djclarke92/nimrod/images/dead_robot.png

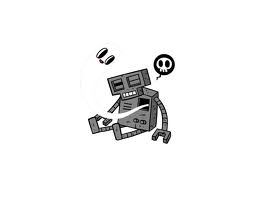
images/dead_robot.png
