djclarke92/nimrod/images/esp8266.png

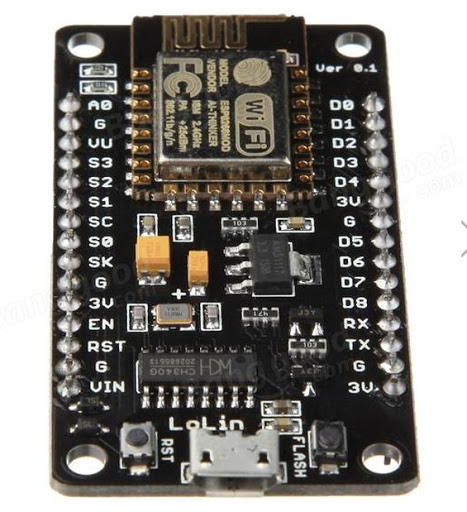
images/esp8266.png
