djclarke92/nimrod/images/eye.png

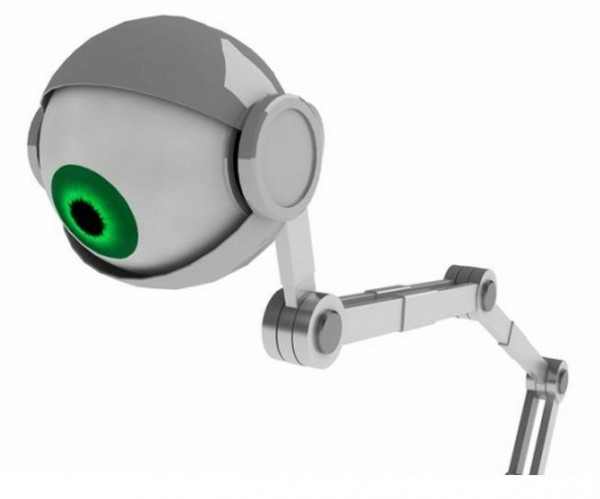
images/eye.png
