djclarke92/nimrod/images/green_tick.png

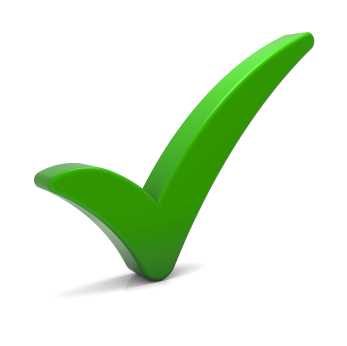
images/green_tick.png
