djclarke92/nimrod/images/inductor2.png

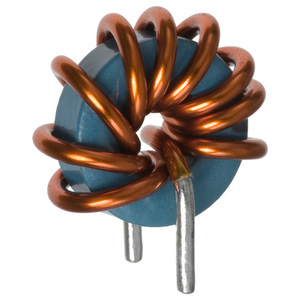
images/inductor2.png
