djclarke92/nimrod/images/questionmark.png

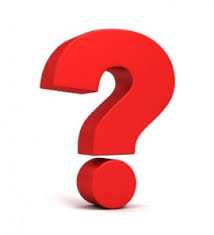
images/questionmark.png
