djclarke92/nimrod/images/usb-rs485.jpg

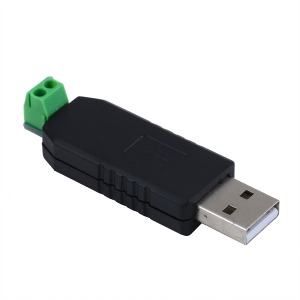
images/usb-rs485.jpg
