djclarke92/nimrod/images/WP3082ADAM.jpg

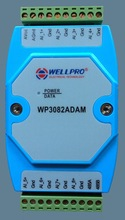
images/WP3082ADAM.jpg
