djclarke92/nimrod/images/WP8025ADAM.jpg

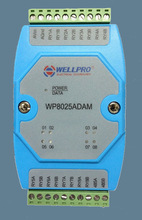
images/WP8025ADAM.jpg
