djclarke92/nimrod/bin/set-address.cpp

/*
 * Nimrod set-address utility: set the modbus address and baud rate on Wellpro modbus devices
 *
 */

#include <stdio.h>
#include <unistd.h>
#include <string.h>
#include <stdlib.h>
#include <errno.h>
#include <signal.h>
#include <stdarg.h>
#include <time.h>
#include <sys/stat.h>
#include <pthread.h>
#include <sys/wait.h>

#include <modbus/modbus.h>


int gRS485_iBaud = 9600;
char gRS485_cParity = 'N';
int gRS485_iDataBits = 8;
int gRS485_iStopBits = 1;


void SetNewAddress( modbus_t *ctx, int oldAddr, int newAddr, int oldBaud, int newBaud, int type, int vsdOperation );
void ReadData( modbus_t *ctx, int newAddr, int newBaud, int type, int vsdOperation, int vsdValue );


int main( int argc, char** argv )
{
	int type = 0;
	int oldAddr = 0;
	int newAddr = 0;
	int oldBaud = 9600;
	int newBaud = 9600;
	int vsdOperation = 0;
	int vsdValue = 0;
	modbus_t* ctx = NULL;

	printf( "Compiled against libmodbus v%s\n", LIBMODBUS_VERSION_STRING );
	printf( "Linked against libmodbus v%d.%d.%d\n", libmodbus_version_major, libmodbus_version_minor, libmodbus_version_micro );
	printf( "\n" );

	if ( argc >= 7 )
	{	// broadcast new address for ALL connected devices

		oldAddr = atoi( argv[2] );
		newAddr = atoi( argv[3] );
		oldBaud = atoi( argv[4] );
		newBaud = atoi( argv[5] );
		type = atoi( argv[6] );

		if ( argc >= 8 )
			vsdOperation = atoi(argv[7] );
		if ( argc >= 9 )
			vsdValue = atoi(argv[8] );

		gRS485_iBaud = oldBaud;

		ctx = modbus_new_rtu( argv[1], gRS485_iBaud, gRS485_cParity, gRS485_iDataBits, gRS485_iStopBits );
		if ( ctx == NULL )
		{
			printf( "Error: modbus ctx in is null, aborting: %s\n", modbus_strerror(errno) );
			exit( 1 );
		}

		modbus_set_debug(ctx, true);

		if ( modbus_connect(ctx) == -1 )
		{
			printf( "Error: modbus_connect() failed, aborting: %s\n", modbus_strerror(errno) );
			exit( 1 );
		}

		printf( "Ctx %p (vsdOp %d)\n", ctx, vsdOperation );


		SetNewAddress( ctx, oldAddr, newAddr, oldBaud, newBaud, type, vsdOperation );

		if ( oldBaud != newBaud )
		{
			modbus_free( ctx );
			ctx = NULL;

			gRS485_iBaud = newBaud;

			ctx = modbus_new_rtu( argv[1], gRS485_iBaud, gRS485_cParity, gRS485_iDataBits, gRS485_iStopBits );
			if ( ctx == NULL )
			{
				printf( "Error: modbus ctx in is null, aborting: %s\n", modbus_strerror(errno) );
				exit( 1 );
			}

			modbus_set_debug(ctx, true);

			if ( modbus_connect(ctx) == -1 )
			{
				printf( "Error: modbus_connect() failed, aborting: %s\n", modbus_strerror(errno) );
				exit( 1 );
			}

			printf( "Ctx %p, Baud Rate %d\n", ctx, newBaud );
		}

		ReadData( ctx, newAddr, newBaud, type, vsdOperation, vsdValue );


		modbus_free( ctx );
		ctx = NULL;
	}
	else
	{
		printf( "Usage: '%s <com_port> <old_addr> <new_addr> <old_baud> <new_baud> <device_type> [vsd_op] [vsd_val]' to set comms parameters\n", argv[0] );
		printf( "    where device_type: 0 Digital Input devices\n" );
		printf( "                       1 Digital Output devices\n" );
		printf( "                       2 Voltage device and temperature devices\n" );
		printf( "                       3 Thermocouple devices PD3064\n" );
		printf( "                       4 HDL300 water level sensor\n" );
		printf( "                       5 Rotary Encoder MT-5208 series\n" );
		printf( "                       6 PZEM-016 AC V/A Monitor\n" );
		printf( "                       7 NFlixen 9600 VSD\n" );
		printf( "                       8 Power Electronics SD700 VSD\n" );
		printf( "                       9 HDHK 8Ch Current Meter\n" );
		printf( "                      10 SHT40 / XY-MD02 Temperature/Humidity sensor\n" );
		printf( "                      11 PT113MB Load Cell Transmitter\n" );
		printf( "                      12 HPT604 level sensor\n" );
		printf( "                      13 HRS10 rain sensor\n" );
		printf( "    optional   vsd_op: 1 forward\n");
		printf( "                       2 backward\n");
		printf( "                       3 forward jog\n");
		printf( "                       4 backward jog\n");
		printf( "                       5 free stop\n");
		printf( "                       6 speed down stop\n");
		printf( "                       7 fault reset\n");
		printf( "                       8 set frequency\n");
		printf( "              vsd_val: xx frequency in Hz <= 50\n");
	}

	return 0;
}

// PT113MB - baud rate and address set by ATCom windows woftware only
// 0x03 read holding registers
// 0x10 preset multiple registers
// read 40001:	weight/force/count
// read 40003: status

// SHT40 / XY-MD02 Temperature/Humidity sensor
// input register 0x0001	Temprature, 2 bytes
// input register 0x0002	Humidity, 2 bytes
// output register 0x0101	Address, 2 bytes
// output register 0x0102	Baud Rate, 9600, 14400, 19200
// output register 0x0103	Temperature correction / 10, +10.0 - -10.0, 2 bytes
// output register 0x0104	Humidity correction / 10, +10.0 - -10.0, 2 bytes


// PZEM-016 AC V/I Monitor
// Does not reply to the broadcast address 0x00
// Uses read_input_registers()
// Only 9600 baud is supported
// Input Register 0x00 voltage, lsb = 0.1V
// Input Register 0x01/2 current, lsb = 0.001A
// Input Register 0x03/4 power, lsb = 0.1W
// Input Register 0x05/6 energy, lsb = 1Wh
// Input Register 0x07 frequency, lsb = 0.1Hz
// Input Register 0x08 power factor, lsb = 0.01
// Input Register 0x09 alarm status
// Register 0x01 power alarm threshold
// Register 0x02 address
//
// MT 5208 Rotary Encoder 12 bit
// function code 0x03 = read
// Register 0x00 angle
// Register 0x01 turns
// Register 0x02 address
// Register 0x03 baud rate (1=9600, 2=19200, 3=38400)
// Register 0x04 parity (1=N, 2=Odd, 3=even)
// Register 0x05 set zero pos (write data 0xff)
// Register 0x06 set counting dir (1=clockwise, 2=anticlockwise)
// Cable red = +12V
//       black = 0V
//       green = rs485A
//       yellow - rs486B
//       white = factory reset (connect to 0V during use)

// HDL300 water level sensor
// function code 0x03 = read
// Register 0x00 = modbus address
// Register 0x01 = baud rate
// Register 0x02 = pressure units (0=Mpa, 1= Kpa, 2=pa, 3=bar, 4=Mbar, 5=kg/cm2, 6= psi, 7=m h2o, 8=mm h2o)
// Register 0x03 = decimal place (0= xxxx, 1= xxx.x, 2= xx.xx, 3= x.xxx, 4= .xxxx)
// Register 0x04 = depth in units (-32768 to 32767)
// Cable red = +12V
//       black = 0V
//       white = rs485B
//       blue = rs485A

// PD30xx sereies devices (thermocouple)
// function code 0x03 = read, 0x06 = write
// Register 0x10: 0x01 (address) 0x00 (comms)
//		address		0x01 to 250
//		comms	bits 7:5 - 	0x00
//				bits 4:3 - 	00 = no parity
//							01 = even parity
//							10 = odd parity
//							11 = odd parity
//				bits 2:0 -	000=9600 	0
//							001=1200	1
//							010=2400	2
//							011=4800	3
//							100=9600	4
//							101=14400	5
//							110=19200	6
// Register 0x11: 0xff (round values) 0x05 (sample rate)
//		rounding		0xff
//		sample rate		0-255 seconds (0 same as 1)

// HDHK 8CH Current Meter
// function code 0x03 read single registers
// function code 0x06 write single register
// function code 0x10 write multiple registers
// register 0x0000 r/o - program version 650 = 6.50
// register 0x0001 r/o - current A-D (ch 01-04) channel range, unsigned int, 40 = 40A
// register 0x0002 r/o - current E-H (ch 05-08) channel range, unsigned int, 40 = 40A
// register 0x0003 r/w - address and baud rate, default 0x0001
//                       high byte high nibble:  0-3 N81, E81, O81, N82
//                       high byte low nibble: 0-8 9600, 1200, 2400, 4800, 9600, 19200, 38200, 57600, 115200
//                       low byte: module address
// register 0x0004 r/o - factory date - high byte year, low byte month
// register 0x0005 - reserved
// register 0x0006 r/w - freq division coefficient(1 - 5, def = 5), sample freq = 10Hz * 5 / coeff, sample freq = 400Hz
// register 0x0007 r/w -  high byte measurement result value, low byte is freq selection coefficient
// register 0x0008 - 0x000F r/o - channel A-H current, unsigned, 0.01A
// register 0x0010 - 0x0017 r/o - channel A-H frequency, unsigned, 0.1Hz
// register 0x0018 - 0x001F r/w - channel A-H current transformer ratio, unsigned 

// HPT604 level sensor
// register 0x0000 2 bytes, sensor type 0-65535
// register 0x0001 2 bytes, address 1-255
// register 0x0002 2 bytes, baud rate 0=19200, 1=9600, 2=4800, 3=2400, 4=1200
// register 0x0003 2 bytes, parity, 0=O, 1=N, 2=E
// register 0x0004 2 bytes, density of medium 1000=water
// register 0x0007 2 bytes, display level unit 16=m, 17=cm, 18=mm
// register 0x0013 4 bytes, level value
// register 0x0015 2 bytes, decimal points of level display

// HRS10 rain sensor - default address 0x01, default baud 4800
// register 0x0000 2 bytes, 10 actual value in mm
// register 0x0000 2 bytes, clear rainfall data semd 0x00 ox5A
// register 0x07D0 2 bytes, modbus address
// retuster 0x07D1 2 bytes, baud rate (0=2400, 1=4800, 2=9600, 3=19200, 4=38400, 5=57600, 6=115200, 7=1200) 

void SetNewAddress( modbus_t *ctx, int oldAddr, int newAddr, int oldBaud, int newBaud, int type, int vsdOperation )
{
	bool bBaudOk = true;
	int modBaud = 2;
	int modBaud2 = 0;
	int modBaud3 = 0;
	int modBaud4 = 0;
	int modBaud5 = 0;
	int modBaudHDHK = 0;
	int modBaudHPT604 = 0;
	int modBaudHRS10 = 0;
	int reg;

	// check the baud rate
	switch ( newBaud )
	{
	default:
		bBaudOk = false;
		break;
	case 4800:
		modBaud = 1;
		modBaud2 = 3;
		modBaud4 = 2;
		modBaudHDHK = 3;
		modBaudHPT604 = 2;
		modBaudHRS10 = 1;
		break;
	case 9600:		// no baud rate change
		modBaud = 2;
		modBaud2 = 0;
		modBaud4 = 3;
		modBaud5 = 1;
		modBaudHDHK = 0;
		modBaudHPT604 = 1;
		modBaudHRS10 = 2;
		break;
	case 19200:
		modBaud = 3;
		modBaud2 = 6;
		modBaud4 = 4;
		modBaud5 = 2;
		modBaudHDHK = 5;
		modBaudHPT604 = 0;
		modBaudHRS10 = 3;
		break;
	}

	switch ( oldBaud )
	{
	default:
		break;
	case 4800:
		modBaud3 = 3;
		break;
	case 9600:		// no baud rate change
		modBaud3 = 0;
		break;
	case 19200:
		modBaud3 = 6;
		break;
	}

	if ( newAddr <= 0x00 || newAddr > 0xfe )
	{	// error
		printf( "Error: Invalid new address %d\n", newAddr );
	}
	else if ( !bBaudOk )
	{
		printf( "Error: Invalid new baud rate %d\n", newBaud );
	}
	else if ( newAddr == oldAddr && newBaud == oldBaud && vsdOperation == 0 )
	{
		printf( "Nothing to set 0x%02x, %d\n", newAddr, newBaud );
	}
	else
	{	// data is valid

		// MODBUS_BROADCAST_ADDRESS;
		if ( modbus_set_slave( ctx, oldAddr ) == -1 )
		{
			printf( "Error: modbus_set_slave(%d) failed: %s\n", oldAddr, modbus_strerror(errno) );
		}


		if ( type == 0 || type == 1 || type == 2 )
		{
			if ( newAddr != oldAddr )
			{
				printf( "Setting new address 0x%02x -> 0x%02x\n", oldAddr, newAddr );

				reg = 0x64;
				if ( modbus_write_register( ctx, reg, newAddr ) == -1 )
				{
					printf( "Error: modbus_write_register(0x%x) failed: %s\n", reg, modbus_strerror(errno) );
				}
				else
				{
					printf( "New slave address 0x%02x set\n", newAddr );

					if ( modbus_set_slave( ctx, newAddr ) == -1 )
					{
						printf( "Error: modbus_set_slave(%d) failed: %s\n", newAddr, modbus_strerror(errno) );
					}
				}
			}
			else
			{
				printf( "Warning: skip setting module address\n" );
			}

			if ( newBaud != oldBaud )
			{
				printf( "Setting new baud rate %d -> %d (%d)\n", oldBaud, newBaud, modBaud );

				reg = 0x65;
				if ( modbus_write_register( ctx, reg, modBaud ) == -1 )
				{
					printf( "Error: modbus_write_register(0x%x) failed: %s\n", reg, modbus_strerror(errno) );
				}
				else
				{
					printf( "New baud rate %d set\n", newBaud );
				}
			}
		}
		else if ( type == 3 )
		{	// thermocouple
			if ( newAddr != oldAddr )
			{
				int val = modBaud3;	// 0x00 = 9600 baud in low byte

				val += (newAddr << 8);

				printf( "Setting new address 0x%02x -> 0x%02x (0x%x)\n", oldAddr, newAddr, val );

				reg = 0x10;
				if ( modbus_write_register( ctx, reg, val ) == -1 )
				{
					printf( "Error: modbus_write_register(0x%x) failed: %s\n", reg, modbus_strerror(errno) );
				}
				else
				{
					printf( "New slave address 0x%02x set\n", newAddr );

					if ( modbus_set_slave( ctx, newAddr ) == -1 )
					{
						printf( "Error: modbus_set_slave(%d) failed: %s\n", newAddr, modbus_strerror(errno) );
					}
				}
			}
			else
			{
				printf( "Warning: skip setting module address\n" );
			}

			if ( newBaud != oldBaud )
			{
				int val = modBaud2;
				val += (newAddr << 8);

				printf( "Setting new baud rate %d -> %d (%d,0x%x)\n", oldBaud, newBaud, modBaud2, val );

				reg = 0x10;
				if ( modbus_write_register( ctx, reg, val ) == -1 )
				{
					printf( "Error: modbus_write_register(0x%x) failed: %s\n", reg, modbus_strerror(errno) );
				}
				else
				{
					printf( "New baud rate %d set\n", newBaud );
				}
			}
		}
		else if ( type == 4 )
		{	// HDL300 level sensor

			if ( newAddr != oldAddr )
			{
				printf( "Setting new address 0x%02x -> 0x%02x\n", oldAddr, newAddr );

				// HDL300 modbus address is in register 0x00
				reg = 0x00;
				if ( modbus_write_register( ctx, reg, newAddr ) == -1 )
				{
					printf( "Error: modbus_write_register(0x%x) failed: %s\n", reg, modbus_strerror(errno) );
				}
				else
				{
					printf( "New slave address 0x%02x set\n", newAddr );

					if ( modbus_set_slave( ctx, newAddr ) == -1 )
					{
						printf( "Error: modbus_set_slave(%d) failed: %s\n", newAddr, modbus_strerror(errno) );
					}
				}
			}
			else
			{
				printf( "Warning: skip setting module address\n" );
			}

			if ( newBaud != oldBaud )
			{
				printf( "Setting new baud rate %d -> %d (%d)\n", oldBaud, newBaud, modBaud4 );

				reg = 0x1;
				if ( modbus_write_register( ctx, reg, modBaud4 ) == -1 )
				{
					printf( "Error: modbus_write_register(0x%x) failed: %s\n", reg, modbus_strerror(errno) );
				}
				else
				{
					printf( "New baud rate %d set\n", newBaud );
				}
			}

			if ( newAddr != oldAddr || newBaud != oldBaud )
			{	// write changes to eeprom
				usleep( 50000 );

				reg = 0x0f;
				if ( modbus_write_register( ctx, reg, 0x0000) == -1 )
				{
					printf( "Error: modbus_write_register(0x%x) failed: %s\n", reg, modbus_strerror(errno) );
				}
				else
				{
					printf( "Changes saved\n" );
				}

				usleep( 200000 );
			}
		}
		else if ( type == 5 )
		{	// rotary encoder
			if ( newAddr != oldAddr )
			{
				printf( "Setting new address 0x%02x -> 0x%02x\n", oldAddr, newAddr );

				// MT-5208 modbus address is in register 0x02
				reg = 0x02;
				if ( modbus_write_register( ctx, reg, newAddr ) == -1 )
				{
					printf( "Error: modbus_write_register(0x%x) failed: %s\n", reg, modbus_strerror(errno) );
				}
				else
				{
					printf( "New slave address 0x%02x set\n", newAddr );

					if ( modbus_set_slave( ctx, newAddr ) == -1 )
					{
						printf( "Error: modbus_set_slave(%d) failed: %s\n", newAddr, modbus_strerror(errno) );
					}
				}
			}
			else
			{
				printf( "Warning: skip setting module address\n" );
			}

			if ( newBaud != oldBaud )
			{
				printf( "Setting new baud rate %d -> %d (%d)\n", oldBaud, newBaud, modBaud5 );

				reg = 0x03;
				if ( modbus_write_register( ctx, reg, modBaud5 ) == -1 )
				{
					printf( "Error: modbus_write_register(0x%x) failed: %s\n", reg, modbus_strerror(errno) );
				}
				else
				{
					printf( "New baud rate %d set\n", newBaud );
				}
			}
		}
		else if ( type == 6 )
		{	// PZEM-016 AC V/I Monitor
			if ( newAddr != oldAddr )
			{
				printf( "Setting new address 0x%02x -> 0x%02x\n", oldAddr, newAddr );

				// MT-5208 modbus address is in register 0x02
				reg = 0x02;
				if ( modbus_write_register( ctx, reg, newAddr ) == -1 )
				{
					printf( "Error: modbus_write_register(0x%x) failed: %s\n", reg, modbus_strerror(errno) );
				}
				else
				{
					printf( "New slave address 0x%02x set\n", newAddr );

					if ( modbus_set_slave( ctx, newAddr ) == -1 )
					{
						printf( "Error: modbus_set_slave(%d) failed: %s\n", newAddr, modbus_strerror(errno) );
					}
				}
			}
			else
			{
				printf( "Warning: skip setting module address\n" );
			}

			if ( newBaud != oldBaud )
			{
				printf( "Only supports 9600 baud %d\n", oldBaud );
			}
		}
		else if ( type == 7 || type == 8 )
		{	// NFlixen VSD - baud rate set on the VSD
			// Power Electronics VSD
			if ( newBaud != oldBaud )
			{
				printf( "Ignoring baud rate change\n" );
			}
		}
		else if ( type == 9 )
		{	// HDHK 8Ch current meter
			if ( newAddr != oldAddr || newBaud != oldBaud )
			{
				reg = 0x0003;

				uint16_t parms = ((0x00 * 0x0f) << 12);	// N81
				uint16_t val = parms + ((modBaudHDHK & 0x0f) << 8) + parms + (newAddr & 0xff);

				if ( modbus_write_register( ctx, reg, val ) == -1 )
				{
					printf( "Error: modbus_write_register(0x%x) failed: %s\n", reg, modbus_strerror(errno) );
				}
				else
				{
					if ( newAddr != oldAddr )
					{
						printf( "New slave address 0x%02x set\n", newAddr );

						if ( modbus_set_slave( ctx, newAddr ) == -1 )
						{
							printf( "Error: modbus_set_slave(%d) failed: %s\n", newAddr, modbus_strerror(errno) );
						}
					}
					if ( newBaud != oldBaud )
					{
						printf( "New baud rate %d set, sleep 3 sec\n", newBaud );
						usleep( 3000000 );
					}
				}

				usleep( 50000 );
			}
		}
		else if ( type == 10 )
		{	// SHT40 / XY-MD02 temperature/humidity sensor
			if ( newAddr != oldAddr || newBaud != oldBaud )
			{
				reg = 0x0101;

				uint16_t val[2];

				val[0] = newAddr;
				switch ( newBaud )
				{
				default:
				case 9600:
					val[1] = 9600;
					break;
				case 14400:
					val[1] = 14400;
					break;
				case 19200:
					val[1] = 19200;
					break;
				}

				if ( modbus_write_registers( ctx, reg, 2, val ) == -1 )
				{
					printf( "Error: modbus_write_register(0x%x) failed: %s\n", reg, modbus_strerror(errno) );
				}
				else if ( newAddr == oldAddr )
				{
					printf( "New baud rate %d set\n", newBaud );
				}
				else if ( newBaud == oldBaud )
				{
					printf( "New slave address 0x%02d set\n", newAddr );
				}
				else
				{
					printf( "New slave address 0x%02d set\n", newAddr );
					printf( "New baud rate %d set\n", newBaud );
				}
			}

			// must power cycle the device when changing the address of baud rate
			if ( newAddr != oldAddr || newBaud != oldBaud )
			{
				printf( "\nXY-MD02 device does NOT listen to broadcast address 0x00, default addr is 0x01\n" );
				printf( "\nPower cycle the device to set the new address / baud rate\nPress enter when done\n");
				getc(stdin);
			}
		}
		else if ( type == 11 )
		{
			printf( "skip baud/address setting for PT113MB\n" );
		}
		else if ( type == 12 )
		{	// HPT602 level sensor

			if ( newAddr != oldAddr )
			{
				printf( "Setting new address 0x%02x -> 0x%02x\n", oldAddr, newAddr );

				// HPT604 modbus address is in register 0x0001
				reg = 0x01;
				if ( modbus_write_register( ctx, reg, newAddr ) == -1 )
				{
					printf( "Error: modbus_write_register(0x%x) failed: %s\n", reg, modbus_strerror(errno) );
				}
				else
				{
					printf( "New slave address 0x%02x set\n", newAddr );

					if ( modbus_set_slave( ctx, newAddr ) == -1 )
					{
						printf( "Error: modbus_set_slave(%d) failed: %s\n", newAddr, modbus_strerror(errno) );
					}
				}
			}
			else
			{
				printf( "Warning: skip setting module address\n" );
			}

			if ( newBaud != oldBaud )
			{
				printf( "Setting new baud rate %d -> %d (%d)\n", oldBaud, newBaud, modBaudHPT604 );

				reg = 0x02;
				if ( modbus_write_register( ctx, reg, modBaudHPT604 ) == -1 )
				{
					printf( "Error: modbus_write_register(0x%x) failed: %s\n", reg, modbus_strerror(errno) );
				}
				else
				{
					printf( "New baud rate %d set\n", newBaud );
				}
			}
		}
		else if ( type == 13 )
		{	// HRS10 rain sensor sensor

			if ( newAddr != oldAddr )
			{
				printf( "Setting new address 0x%02x -> 0x%02x\n", oldAddr, newAddr );

				// HPT604 modbus address is in register 0x0001
				reg = 0x07D0;
				if ( modbus_write_register( ctx, reg, newAddr ) == -1 )
				{
					printf( "Error: modbus_write_register(0x%x) failed: %s\n", reg, modbus_strerror(errno) );
				}
				else
				{
					printf( "New slave address 0x%02x set\n", newAddr );

					if ( modbus_set_slave( ctx, newAddr ) == -1 )
					{
						printf( "Error: modbus_set_slave(%d) failed: %s\n", newAddr, modbus_strerror(errno) );
					}
				}
			}
			else
			{
				printf( "Warning: skip setting module address\n" );
			}

			if ( newBaud != oldBaud )
			{
				printf( "Setting new baud rate %d -> %d (%d)\n", oldBaud, newBaud, modBaudHRS10 );

				reg = 0x07D1;
				if ( modbus_write_register( ctx, reg, modBaudHRS10 ) == -1 )
				{
					printf( "Error: modbus_write_register(0x%x) failed: %s\n", reg, modbus_strerror(errno) );
				}
				else
				{
					printf( "New baud rate %d set\n", newBaud );
				}
			}
		}
		else
		{
			printf( "Error: invalid type = %d\n", type );
		}
	}

	usleep( 30000 );
}

void ReadData( modbus_t *ctx, int newAddr, int newBaud, int type, int vsdOperation, int vsdValue )
{
	int rc;
	int addr;
	int iLen = 8;

	if ( type == 0 )
	{
		printf( "Setting slave addr to %d\n", newAddr );
		if ( modbus_set_slave( ctx, newAddr ) == -1 )
		{
			printf( "Error: modbus_set_slave(%d) failed: %s\n", newAddr, modbus_strerror(errno) );
		}

		usleep( 30000 );

		// read input bits to see if the device is talking
		addr = 0;
		uint8_t uInputs[iLen];

		for ( int i = 0; i < iLen; i++ )
		{
			uInputs[i] = 0;
		}

		rc = modbus_read_input_bits( ctx, addr, iLen, uInputs );
		if ( rc == -1 )
		{
			printf( "Error: modbus_read_input_bits() failed: %s\n", modbus_strerror(errno) );
		}
		else
		{
			printf( "Read registers: " );
			for ( int i = 0; i < iLen; i++ )
			{
				printf( "%u ", uInputs[i] );
			}
			printf ( "\n" );
		}
	}
	else if ( type == 1 )
	{	// output
		printf( "Setting slave addr to %d\n", newAddr );
		if ( modbus_set_slave( ctx, newAddr ) == -1 )
		{
			printf( "Error: modbus_set_slave(%d) failed: %s\n", newAddr, modbus_strerror(errno) );
		}

		usleep( 30000 );

		printf( "modbus_write_bit() 1 -> 1\n" );
		if ( modbus_write_bit( ctx, 1, true ) == -1 )
		{	// failed
			printf( "Error: modbus_write_bit() failed: %s\n", modbus_strerror(errno) );
		}
		else
		{
			printf( "Bit 1 turned on\n" );
		}
		usleep( 500000 );

		uint8_t cData[16];
		printf( "modbus_read_bits()\n" );
		if ( modbus_read_bits( ctx, 0, 16, cData ) == -1 )
		{	// error
			printf( "Error: modbus_read_bits() failed: %s\n", modbus_strerror(errno) );
		}
		else
		{
			printf( "Read bits: " );
			for ( int i = 0; i < iLen; i++ )
			{
				printf( "%u ", (uint8_t)cData[i] );
			}
			printf ( "\n" );
		}

		usleep( 30000 );

		printf( "modbus_write_bit() 1 -> 0\n" );
		if ( modbus_write_bit( ctx, 1, false ) == -1 )
		{	// failed
			printf( "Error: modbus_write_bit() failed: %s\n", modbus_strerror(errno) );
		}
		else
		{
			printf( "Bit 1 turned off\n" );
		}
	}
	else if ( type == 2 )
	{	// voltage
		printf( "Setting slave addr to %d\n", newAddr );
		if ( modbus_set_slave( ctx, newAddr ) == -1 )
		{
			printf( "Error: modbus_set_slave(%d) failed: %s\n", newAddr, modbus_strerror(errno) );
		}

		addr = 0x00;
		uint16_t ulInputs[iLen];

		rc = modbus_read_registers( ctx, addr, iLen, ulInputs );
		if ( rc == -1 )
		{
			printf( "Error: modbus_read_registers() failed: %s\n", modbus_strerror(errno) );
		}
		else
		{
			printf( "Read registers: " );
			for ( int i = 0; i < iLen; i++ )
			{
				printf( "%u ", ulInputs[i] );
			}
			printf ( "\n" );
		}
	}
	else if ( type == 3 )
	{	// thermocouple
		printf( "Setting slave addr to %d\n", newAddr );
		if ( modbus_set_slave( ctx, newAddr ) == -1 )
		{
			printf( "Error: modbus_set_slave(%d) failed: %s\n", newAddr, modbus_strerror(errno) );
		}

		addr = 0x20;
		uint16_t ulInputs[iLen];

		rc = modbus_read_registers( ctx, addr, iLen, ulInputs );
		if ( rc == -1 )
		{
			printf( "Error: modbus_read_registers() failed: %s\n", modbus_strerror(errno) );
		}
		else
		{
			printf( "Read registers: " );
			for ( int i = 0; i < iLen; i++ )
			{
				printf( "%u ", ulInputs[i] );
			}
			printf ( "\n" );
		}
	}
	else if ( type == 4 )
	{	// hdl300 water level
		printf( "Setting slave addr to %d\n", newAddr );
		if ( modbus_set_slave( ctx, newAddr ) == -1 )
		{
			printf( "Error: modbus_set_slave(%d) failed: %s\n", newAddr, modbus_strerror(errno) );
		}

		uint16_t ulInputs[iLen];

		int iFactor = 1;

		iLen = 2;
		addr = 0x02;
		rc = modbus_read_registers( ctx, addr, iLen, ulInputs );
		if ( rc == -1 )
		{
			printf( "Error: modbus_read_registers() failed: %s\n", modbus_strerror(errno) );
		}
		else
		{
			printf( "Read registers: 0x%02x (units)  0x%02x (decimal)\n", ulInputs[0], ulInputs[1] );
			
			// TODO: iFactor needs to change depending on what units are being read. This code assume units=7 (m h2o)
			// check decimal point
			switch ( ulInputs[1] )
			{
			default:
				break;
			case 0:	// xxxx
				iFactor = 1000;
				break;
			case 1:	// xxx.x
				iFactor = 100;
				break;
			case 2:	// xx.xx
				iFactor = 10;
				break;
			case 3:	// x.xxx
				iFactor = 1;
				break;
			}
		}

		addr = 0x04;

		rc = modbus_read_registers( ctx, addr, iLen, ulInputs );
		if ( rc == -1 )
		{
			printf( "Error: modbus_read_registers() failed: %s\n", modbus_strerror(errno) );
		}
		else
		{
			printf( "Read registers: " );
			for ( int i = 0; i < iLen; i++ )
			{
				printf( "%u ", ulInputs[i] );
			}
			printf ( "\n" );
			printf( "Depth = %d mm\n", ulInputs[0] * iFactor );
		}

		usleep( 50000 );

	}
	else if ( type == 5 )
	{	// rotary encoder
		printf( "Setting slave addr to %d\n", newAddr );
		if ( modbus_set_slave( ctx, newAddr ) == -1 )
		{
			printf( "Error: modbus_set_slave(%d) failed: %s\n", newAddr, modbus_strerror(errno) );
		}

		iLen = 5;

		addr = 0x00;
		uint16_t ulInputs[iLen];

		rc = modbus_read_registers( ctx, addr, iLen, ulInputs );
		if ( rc == -1 )
		{
			printf( "Error: modbus_read_registers() failed: %s\n", modbus_strerror(errno) );
		}
		else
		{
			printf( "Read registers: " );
			for ( int i = 0; i < iLen; i++ )
			{
				printf( "%u ", ulInputs[i] );
			}
			printf ( "\n" );
			printf( "Angle %d (%.1f deg), Turns %d\n", ulInputs[0], 360 * (double)ulInputs[0]/4096, ulInputs[1] );
		}
	}
	else if ( type == 6 )
	{	// PZEM-016 AC V/A Monitor
		printf( "Setting slave addr to %d\n", newAddr );
		if ( modbus_set_slave( ctx, newAddr ) == -1 )
		{
			printf( "Error: modbus_set_slave(%d) failed: %s\n", newAddr, modbus_strerror(errno) );
		}

		iLen = 10;

		addr = 0x00;
		uint16_t ulInputs[iLen];

		rc = modbus_read_input_registers( ctx, addr, iLen, ulInputs );
		if ( rc == -1 )
		{
			printf( "Error: modbus_read_registers() failed: %s\n", modbus_strerror(errno) );
		}
		else
		{
			printf( "Read registers: " );
			for ( int i = 0; i < iLen; i++ )
			{
				printf( "%u ", ulInputs[i] );
			}
			printf ( "\n" );
			printf( "V=%.1fV, I=%.2fA, P=%.0fW, E=%dWh, F=%.1fHz, PF=%.1f, Alrm=%d\n", (double)ulInputs[0] / 10, (double)(ulInputs[1] + (ulInputs[2]>>8)) / 1000, (double)(ulInputs[3] + (ulInputs[4]>>8)) / 10,
					(int)(ulInputs[5] + (ulInputs[6]>>8)), (double)ulInputs[7] / 10, (double)ulInputs[8] / 100, ulInputs[9] );
		}
	}
	else if ( type == 7 )
	{	// NFlixen VSD
		int iSleep = 50000;
		printf( "Setting slave addr to %d\n", newAddr );
		if ( modbus_set_slave( ctx, newAddr ) == -1 )
		{
			printf( "Error: modbus_set_slave(%d) failed: %s\n", newAddr, modbus_strerror(errno) );
		}

		iLen = 18;

		addr = 0x1001;
		uint16_t ulInputs[iLen];

		rc = modbus_read_registers( ctx, addr, iLen, ulInputs );
		if ( rc == -1 )
		{
			printf( "Error: modbus_read_registers() failed: %s\n", modbus_strerror(errno) );
		}
		else
		{
			printf( "Read registers: " );
			for ( int i = 0; i < iLen; i++ )
			{
				printf( "%u ", ulInputs[i] );
			}
			printf ( "\n" );
			printf( "F=%.2fHz, BV=%.1fV, MV=%.1fV, MA=%.1fA, MP=%.2fkW, MT=%.1f%%, RS=%.1frpm\n",
					(double)ulInputs[0] / 100,	// 0.01 Hz
					(double)ulInputs[1] / 10, 	// 0.1 V
					(double)ulInputs[2],		// 1 V
					(double)ulInputs[3] / 10, 	// 0.1 A ??
					(double)ulInputs[4] / 100,	// 0.1 kW ??
					(double)ulInputs[5] / 10, 	// 0.1 %
					(double)ulInputs[6] );		// 1
		}
		printf("\n");

		usleep( iSleep );

		// output current
		iLen = 1;
		addr = 0x7004;
		rc = modbus_read_registers( ctx, addr, iLen, ulInputs );
		if ( rc == -1 )
		{
			printf( "Error: modbus_read_registers() failed: %s\n", modbus_strerror(errno) );
		}
		else
		{
				printf( "Read Output Current: %d %.1f A\n", (int)ulInputs[0], (double)ulInputs[0] / 10 );
		}
		printf("\n");

		usleep( iSleep );

		// status 
		iLen = 1;
		addr = 0x3000;

		rc = modbus_read_registers( ctx, addr, iLen, ulInputs );
		if ( rc == -1 )
		{
			printf( "Error: modbus_read_registers() failed: %s\n", modbus_strerror(errno) );
		}
		else
		{
			if ( ulInputs[0] == 1 )
				printf( "Read status: %d Forward\n", (int)ulInputs[0] );
			else if ( ulInputs[0] == 2 )
				printf( "Read status: %d Reverse\n", (int)ulInputs[0] );
			else if ( ulInputs[0] == 3 )
				printf( "Read status: %d Stopped\n", (int)ulInputs[0] );
			else
				printf( "Read status: %d Unknown\n", (int)ulInputs[0] );
		}
		printf("\n");

		usleep( iSleep );

		// fault code
		iLen = 1;
		addr = 0x8000;

		rc = modbus_read_registers( ctx, addr, iLen, ulInputs );
		if ( rc == -1 )
		{
			printf( "Error: modbus_read_registers() failed: %s\n", modbus_strerror(errno) );
		}
		else
		{
			printf( "Read fault code: %d\n", (int)ulInputs[0] );
		}
		printf("\n");

		if ( vsdOperation >= 1 && vsdOperation <= 7 )
		{	// vsd must be set for communications control P0-02 = 2
			// P0-03 = 9 for frequency control by communications
			usleep( iSleep );

			addr = 0x2000;

			rc = modbus_write_register( ctx, addr, vsdOperation );
			if ( rc == -1 )
			{
				printf( "Error: modbus_write_register() failed: %s\n", modbus_strerror(errno) );
			}
			else
			{
				printf( "VSD operation set to %d\n", vsdOperation );
			}
		}
		else if ( vsdOperation == 8 )
		{	// set frequency
			// value is % * 100 of max frequency (50Hz)
			usleep( iSleep );

			addr = 0x1000;

			int val = 10000 * ((double)vsdValue / 50);
			if ( val > 10000 )
				val = 10000;

			rc = modbus_write_register( ctx, addr, val );
			if ( rc == -1 )
			{
				printf( "Error: modbus_write_register() failed: %s\n", modbus_strerror(errno) );
			}
			else
			{
				printf( "VSD operation set to %d, %d Hz -> %d\n", vsdOperation, vsdValue, val );
			}
		}
	}
	else if ( type == 8 )
	{	// Power Electronics VSD
		printf( "Setting slave addr to %d\n", newAddr );
		if ( modbus_set_slave( ctx, newAddr ) == -1 )
		{
			printf( "Error: modbus_set_slave(%d) failed: %s\n", newAddr, modbus_strerror(errno) );
		}

		iLen = 9;

		addr = 40162;
		uint16_t ulInputs[iLen];

		// 0 40162: speed reference, 8192 = 100%
		// 1 40163: motor current, A / 10
		// 2 40164: motor torque, 8192 = 100%
		// 3 40165: motor power, kW / 10
		// 4 40166: motor voltage, V
		// 5 40167: motor frequency, Hz
		// 6 40168: motor power factor, pf /10
		// 7 40169: motor speed, rpm
		// 8 40170: motor speed, 8192 = 100%

		rc = modbus_read_registers( ctx, addr, iLen, ulInputs );
		if ( rc == -1 )
		{
			printf( "Error: modbus_read_registers() failed: %s\n", modbus_strerror(errno) );
		}
		else
		{
			printf( "Read registers: " );
			for ( int i = 0; i < iLen; i++ )
			{
				printf( "%u ", ulInputs[i] );
			}
			printf ( "\n" );
			printf( "F=%.2fHz, MV=%.1fV, MA=%.1fA, MP=%.2fkW, MT=%.1f%%, RS=%.1frpm\n",
					(double)ulInputs[5],		// Hz
					(double)ulInputs[4], 		// V
					(double)ulInputs[1] / 10,	// 0.1 A
					(double)ulInputs[3] / 10,	// 0.1 kW ??
					100 * (double)ulInputs[2] / 8192, 	// %
					(double)ulInputs[7] );		// rpm
		}
		printf("\n");

		usleep( 50000 );

		if ( vsdOperation >= 1 && vsdOperation <= 7 )
		{	// vsd must be set for communications control
			printf( "VSD operation not supported\n" );
		}
	}
	else if ( type == 9 )
	{	// HDHK 8Ch current meter
		printf( "Setting slave addr to %d\n", newAddr );
		if ( modbus_set_slave( ctx, newAddr ) == -1 )
		{
			printf( "Error: modbus_set_slave(%d) failed: %s\n", newAddr, modbus_strerror(errno) );
		}

		iLen = 8;
		uint16_t ulInputs[iLen];

		// read address and baud rate
		addr = 0x0000;
		rc = modbus_read_registers( ctx, addr, iLen, ulInputs );
		if ( rc == -1 )
		{
			printf( "Error: modbus_read_registers() failed: %s\n", modbus_strerror(errno) );
		}
		else
		{
			printf( "Version %.2f\n", (double)ulInputs[0] / 100 );
			printf( "Channel A-D range %dA\n", ulInputs[1] );
			printf( "Channel E-H range %dA\n", ulInputs[1] );
			printf( "Baud Rate %d\n", ((ulInputs[3] & 0x0f00) >> 8) );
			printf( "Address %d\n", (ulInputs[3] & 0x00ff) );
			printf( "Freq Div Coeff %d\n", ulInputs[6] );
		}

		addr = 0x0008;	
		rc = modbus_read_registers( ctx, addr, iLen, ulInputs );
		if ( rc == -1 )
		{
			printf( "Error: modbus_read_registers() failed: %s\n", modbus_strerror(errno) );
		}
		else
		{
			printf( "Read registers: " );
			for ( int i = 0; i < iLen; i++ )
			{
				printf( "%.2fA ", (double)ulInputs[i] / 100 );
			}
			printf ( " current\n" );
		}

		usleep( 30000 );

		addr = 0x0010;	
		rc = modbus_read_registers( ctx, addr, iLen, ulInputs );
		if ( rc == -1 )
		{
			printf( "Error: modbus_read_registers() failed: %s\n", modbus_strerror(errno) );
		}
		else
		{
			printf( "Read registers: " );
			for ( int i = 0; i < iLen; i++ )
			{
				printf( "%.1fHz ", (double)ulInputs[i] / 10 );
			}
			printf ( " measurement frequency\n" );
		}

		usleep( 30000 );

		addr = 0x0018;	
		rc = modbus_read_registers( ctx, addr, iLen, ulInputs );
		if ( rc == -1 )
		{
			printf( "Error: modbus_read_registers() failed: %s\n", modbus_strerror(errno) );
		}
		else
		{
			printf( "Read registers: " );
			for ( int i = 0; i < iLen; i++ )
			{
				printf( "%u ", ulInputs[i] );
			}
			printf ( " current transformer ratio\n" );
		}	
	}
	else if ( type == 10 )
	{	// SHT40 / XY-MD02 temperature / humidity sensor
		printf( "Setting slave addr to %d\n", newAddr );
		if ( modbus_set_slave( ctx, newAddr ) == -1 )
		{
			printf( "Error: modbus_set_slave(%d) failed: %s\n", newAddr, modbus_strerror(errno) );
		}

		iLen = 1;
		uint16_t ulInputs[iLen];
		addr = 0x0001;	
		rc = modbus_read_input_registers( ctx, addr, iLen, ulInputs );
		if ( rc == -1 )
		{
			printf( "Error: modbus_read_input_registers() failed: %s\n", modbus_strerror(errno) );
		}
		else
		{
			printf( "Temperature = %.1f degC\n", (double)((int)ulInputs[0]) / 10 );
		}

		addr = 0x0002;	
		rc = modbus_read_input_registers( ctx, addr, iLen, ulInputs );
		if ( rc == -1 )
		{
			printf( "Error: modbus_read_input_registers() failed: %s\n", modbus_strerror(errno) );
		}
		else
		{
			printf( "Humidity = %.1f %%\n", (double)ulInputs[0] / 10 );
		}
	}
	else if ( type == 11 )
	{	// PT113MB load cell transmitter
		printf( "Setting slave addr to %d\n", newAddr );
		if ( modbus_set_slave( ctx, newAddr ) == -1 )
		{
			printf( "Error: modbus_set_slave(%d) failed: %s\n", newAddr, modbus_strerror(errno) );
		}

		// read the psu voltage
		iLen = 1;
		uint16_t ulInputs[iLen];
		addr = 33;	
		rc = modbus_read_registers( ctx, addr, iLen, ulInputs );
		if ( rc == -1 )
		{
			printf( "Error: modbus_read_registers() failed: %s\n", modbus_strerror(errno) );
		}
		else
		{
			printf( "PSU Voltage %.1f V\n", ((double)ulInputs[0])/10 );
		}

		// read the status
		iLen = 1;
		//uint16_t ulInputs[iLen];
		addr = 2;	
		rc = modbus_read_registers( ctx, addr, iLen, ulInputs );
		if ( rc == -1 )
		{
			printf( "Error: modbus_read_registers() failed: %s\n", modbus_strerror(errno) );
		}
		else
		{
			printf( "Status 0x%04X\n", ulInputs[0] );
			printf( "System %s\n", ((ulInputs[0] & 0x0001) == 0 ? "Ready" : "Busy") );
			printf( "%s\n", ((ulInputs[0] & 0x0002) == 0 ? "Error" : "Data Ok") );
			printf( "Weight %s\n", ((ulInputs[0] & 0x0003) == 0 ? "Stable" : "Unstable") );
			printf( "%s Mode\n", ((ulInputs[0] & 0x0004) == 0 ? "Gross" : "Net") );
			printf( "%s Mode\n", ((ulInputs[0] & 0x0006) == 0 ? "Weight/Force" : "Count") );
			printf( "%s centre of zero\n", ((ulInputs[0] & 0x1000) == 0 ? "Out of" : "Weight is in") );
			printf( "Error Code %s (%d)\n", ((ulInputs[0] & 0xE000) == 0 ? "No Errors" : "Error"), (ulInputs[0] & 0xE000)>>13 );
		}

		// read the weight/count
		iLen = 2;
		uint16_t ulInputs2[iLen];
		addr = 0;	
		rc = modbus_read_registers( ctx, addr, iLen, ulInputs2 );
		if ( rc == -1 )
		{
			printf( "Error: modbus_read_registers() failed: %s\n", modbus_strerror(errno) );
		}
		else
		{
			printf( "Weight/Count %u (%u,%u)\n", 65536*ulInputs2[0] + ulInputs2[1], ulInputs[0], ulInputs[1] );
		}

		// read the operating mode
		iLen = 1;
		//uint16_t ulInputs2[iLen];
		addr = 13;	
		rc = modbus_read_registers( ctx, addr, iLen, ulInputs );
		if ( rc == -1 )
		{
			printf( "Error: modbus_read_registers() failed: %s\n", modbus_strerror(errno) );
		}
		else
		{
			printf( "Operating Mode %u\n", ulInputs[0] );
		}

		// read the count mode input range
		iLen = 1;
		//uint16_t ulInputs2[iLen];
		addr = 14;	
		rc = modbus_read_registers( ctx, addr, iLen, ulInputs );
		if ( rc == -1 )
		{
			printf( "Error: modbus_read_registers() failed: %s\n", modbus_strerror(errno) );
		}
		else
		{
			printf( "Count Mode Input Range %u\n", ulInputs[0] );
		}

		// read the digital filter
		iLen = 1;
		//uint16_t ulInputs2[iLen];
		addr = 15;	
		rc = modbus_read_registers( ctx, addr, iLen, ulInputs );
		if ( rc == -1 )
		{
			printf( "Error: modbus_read_registers() failed: %s\n", modbus_strerror(errno) );
		}
		else
		{
			printf( "Digital Filter %u\n", ulInputs[0] );
		}	
	}
	else if ( type == 12 )
	{	// HPT604 water level
		printf( "Setting slave addr to %d\n", newAddr );
		if ( modbus_set_slave( ctx, newAddr ) == -1 )
		{
			printf( "Error: modbus_set_slave(%d) failed: %s\n", newAddr, modbus_strerror(errno) );
		}

		iLen = 4;
		uint16_t ulInputs[iLen];

		int iFactor = 1;

		iLen = 1;
		addr = 0x15;	// decimal points
		rc = modbus_read_registers( ctx, addr, iLen, ulInputs );
		if ( rc == -1 )
		{
			printf( "Error: modbus_read_registers() failed: %s\n", modbus_strerror(errno) );
		}
		else
		{
			printf( "Read registers: 0x%02x (decimal)\n", ulInputs[0] );
			
			// TODO: iFactor needs to change depending on what units are being read.
			// check decimal point
			switch ( ulInputs[0] )
			{
			default:
				break;
			case 0:	// xxxx
				iFactor = 1;
				break;
			case 1:	// xxx.x
				iFactor = 10;
				break;
			case 2:	// xx.xx
				iFactor = 100;
				break;
			case 3:	// x.xxx
				iFactor = 1000;
				break;
			}
		}

		iLen = 1;
		addr = 0x07;	// display level units
		rc = modbus_read_registers( ctx, addr, iLen, ulInputs );
		if ( rc == -1 )
		{
			printf( "Error: modbus_read_registers() failed: %s\n", modbus_strerror(errno) );
		}
		else
		{
			printf( "Range units %u (16=m, 17=cm, 18=mm)\n", ulInputs[0] );
		}

		iLen = 2;
		addr = 0x13;
		rc = modbus_read_registers( ctx, addr, iLen, ulInputs );
		if ( rc == -1 )
		{
			printf( "Error: modbus_read_registers() failed: %s\n", modbus_strerror(errno) );
		}
		else
		{
			printf( "Read registers: " );
			for ( int i = 0; i < iLen; i++ )
			{
				printf( "%u ", ulInputs[i] );
			}
			printf ( "\n" );
			printf( "Depth = %d mm (factor %d)\n", ((ulInputs[0] >> 16) + ulInputs[1]), iFactor );
		}

		usleep( 50000 );

	}
	else if ( type == 13 )
	{	// HRS10 rain sensor
		printf( "Setting slave addr to %d\n", newAddr );
		if ( modbus_set_slave( ctx, newAddr ) == -1 )
		{
			printf( "Error: modbus_set_slave(%d) failed: %s\n", newAddr, modbus_strerror(errno) );
		}

		iLen = 2;
		uint16_t ulInputs[iLen];

		iLen = 1;
		addr = 0x0000;	// rain in mm x 10
		rc = modbus_read_registers( ctx, addr, iLen, ulInputs );
		if ( rc == -1 )
		{
			printf( "Error: modbus_read_registers() failed: %s\n", modbus_strerror(errno) );
		}
		else
		{
			printf( "Read registers: 0x%02x (decimal)\n", ulInputs[0] );

			printf( "Rain level %.1f mm\n", (double)ulInputs[0] / 10 );
		}

	}
}
